Alsxilva/Azcatl/Documentación/Diagrama de clases/Diagrama de clases Azcatl.png

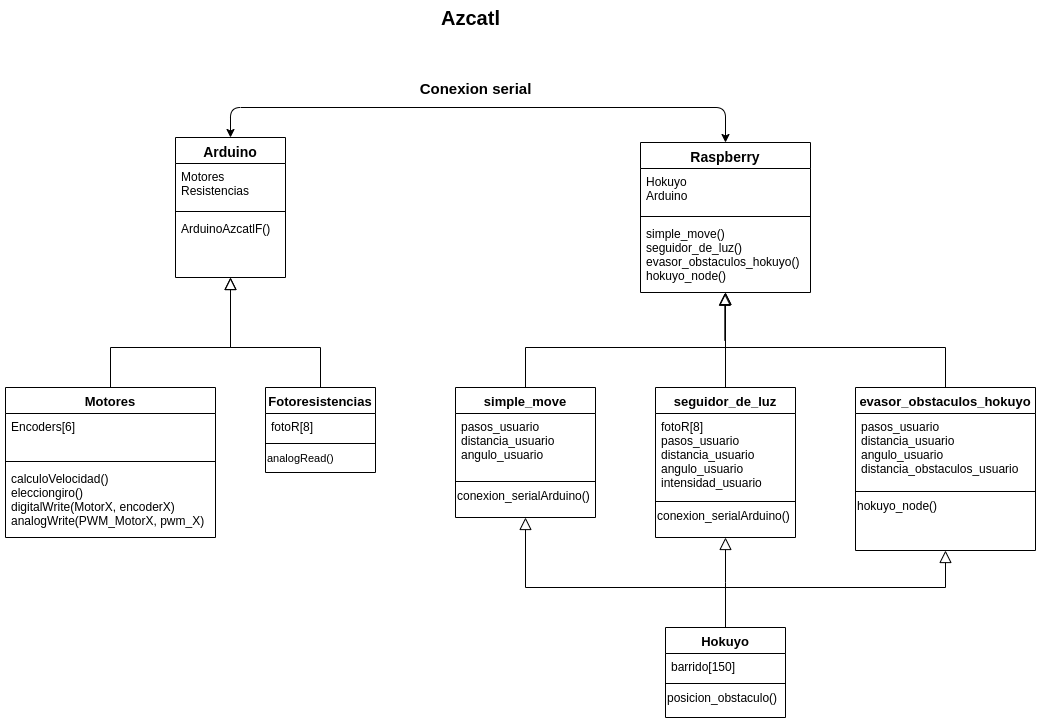
Documentación/Diagrama de clases/Diagrama de clases Azcatl.png
