Alsxilva/Azcatl/Documentación/Máquinas de estado/IMG_5838.JPG

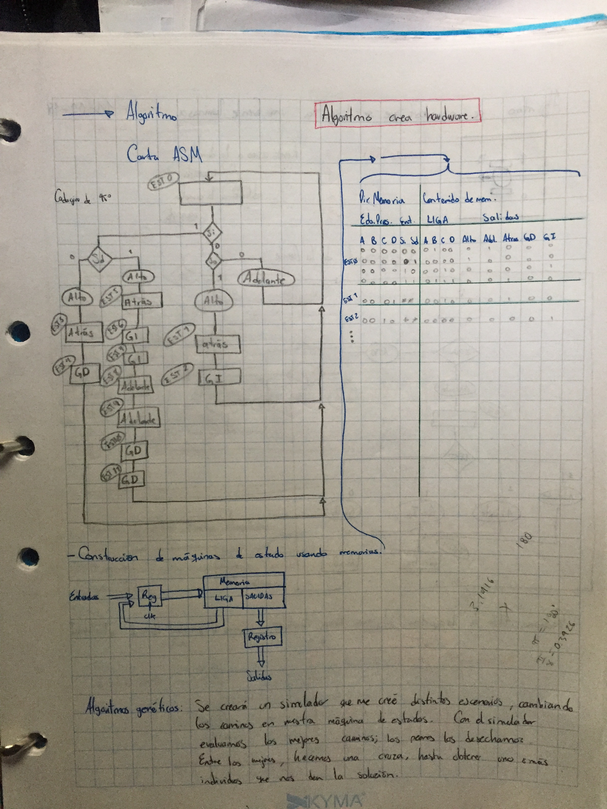
Documentación/Máquinas de estado/IMG_5838.JPG
