Alsxilva/Azcatl/Mis Nodos/evasor_obstaculos_hokuyo_FINAL.cpp

/*-------------------------------------------------------------
Silva Guzmán Alejandro
Dr. Savage Carmona
Agosto 2019

/*--------------------------------------------------------------*/

#include <time.h>
#include <math.h>
#include <stdlib.h>
#include <ros/ros.h>
#include <std_msgs/Int64.h>
#include <std_msgs/Float32.h>
#include <sensor_msgs/LaserScan.h>
#include <std_msgs/Float32MultiArray.h>
	
#define k 			0.1				//Constante de desfase 
#define vm			0.50			//Velocidad maxima [m/s]
#define bw  		0.235			//Ancho de la base del robøt  			[m]
#define ppr			1636.0			//Pulsos por revolucion (Encoder)
#define c_llant 	41.469 			//Circunferencia de cada llantas 		[cm]
#define d_llants	23.50000		//Distancia entre llantas contrarias 	[cm]
#define pi 			3.1415926		//Valor de pi

bool act = false;			 		//Bool para impedir que se avance mientras se gira y viceversa.
bool turnOn = false; 				//(Encender) Bool para evitar que en el primer case avance un paso sin revisar obstaculos-
volatile float enc[2]={0.0,0.0};

/*------------------------------------Encoders------------------------------------*/	

void callbackDer(const std_msgs::Int64::ConstPtr& msg){
	enc[1] = (float)(msg -> data)/ppr;							//Encoder 1 = Encoder derecho
	//printf("%li\n",msg -> data);								//Imprime el valor (float) del encoder
}

void callbackIzq(const std_msgs::Int64::ConstPtr& msg){
	enc[0] = (float)(msg -> data)/ppr;							//Encoder 0 = Encoder izquierdo
	//printf("%li\n",msg -> data);								//Imprime el valor (float) del encoder
	act = true;
}

/*------------------------------------Hokuyo------------------------------------*/	

/*--------------------------------Variables--------------------------------*/	

#define maxRange   80			//Rango de lecturas para el hokuyo
#define minRange  -80								
#define intervalRange  10 		//Grados para cada intervalo

int nuSamples;	 				//Numero de muestras que muestrearemos para detectar el obstaculo mas delgado
int truReadings = 0;				//Contador para obstaculos
int posicion_obstaculo;			//Indica la posicion del obstaculo
float umbral;					//Rango para determinar si se encuentra un obstaculo en determinada posicion
float umbral_usuario;		
float degrees_to_Sample;		//Grados a muestrear para el obstaculo mas delgado con base a la distancia a la que se encuentre y a su ancho
float obstacle_Width;			//Ancho del obstáculo más delgado a detectar	
float promLeft  =	 0;
float promRight =	 0;
float promFront =	 0;
float centralOut, derechaOut, izquierdaOut;
float values[2][(maxRange - minRange) / intervalRange];	//Dos arreglos de 16 valores cada uno

bool hokuyoFlag = false;
bool central_flag, centralDer_flag, centralIzq_flag, derecha_flag, izquierda_flag;		//Banderas para determinar zona de obstaculo

/*--------------------------------Funcion--------------------------------*/	

void callbackHokuyo(const sensor_msgs::LaserScan::ConstPtr &msg){

	int size = ceil((msg -> angle_max - msg -> angle_min) / msg -> angle_increment);	//Redondea al entero de arriba mas cercano. 
	//	size = ceil(593.8181818) = 594 lecturas											//En especifico, redondea a un numero entero el numero de lecturas 
																						//"disponibles" del hokuyoque se mandan desde el nodo "hokuyo_node.py"							
	float sumLeft  = 0;																	
	float sumFront = 0;	
	float sumRight = 0;	
	float values[size];
	
	for(int i = 0 ; i < size ; i++){			//Almacena los valores del hokuyo en un arreglo
		float val = msg -> ranges[i];
		values[i] = msg -> ranges[i];
		
		if(val <= 0.01 && i!=0)					//Evita que se se almacenen valores muy pequeños
			values[i] = 1.2 * values[i-1];
			//float angle = (msg->angle_min+(msg->angle_increment*i))*180.0/3.1415926;
	}

	/*-------------------------------Region central-------------------------------*/

	int centrali[2];
	centralOut = 0;
	float central[]  = {-15,15};		//Rangos para la region central -> Checar documento "Estructura del robot".
		
	centrali[0] = floor((((pi * central[0]) / 180.0) - msg->angle_min) / (msg->angle_increment));	//floor((((pi * -15) / 180) - 1.824262524000698) / 0.006144178739745) = floor(-339.5184288) = -339
	centrali[1] = floor((((pi * central[1]) / 180.0) - msg->angle_min) / (msg->angle_increment));	//floor((((pi *  15) / 180) - 1.824262524000698) / 0.006144178739745) = floor(-254.2997530) = -254
				//Funcion "floor" redondea al entero de abajo mas cercano
				//Esta fracción de codigo se encarga de transformar el ángulo de visión deseado por región a un número (en radianes) para que el hokuyo sea capaz de leerlo.
	
	for(int i = centrali[0]; i < centrali[1]; i++){
		if (values[i] <= umbral)
			truReadings ++;
		else 
			truReadings = 0;
		if (truReadings >= nuSamples){
			central_flag = true;
			truReadings = 0;
			break;
		}
		else
			central_flag = false;
	}

	/*---------------------------Region Izquierda---------------------------*/

	int izquierdai[2];
	izquierdaOut = 0;
	float izquierda[] ={45,75};		//Rangos para la region izquierda -> Checar documento "Estructura del robot".

	izquierdai[0] = floor((((pi * izquierda[0]) / 180.0)-msg->angle_min) / (msg->angle_increment));		//floor((((pi * 45) / 180) - 1.824262524000698) / 0.006144178739745) = floor(-169.0810773) = -169
	izquierdai[1] = floor((((pi * izquierda[1]) / 180.0)-msg->angle_min) / (msg->angle_increment));		//floor((((pi * 75) / 180) - 1.824262524000698) / 0.006144178739745) = floor(-83.86240161) = -83
	
	for(int i = izquierdai[0]; i < izquierdai[1] ; i++){
		if (values[i] <= umbral)
			truReadings ++;
		else 
			truReadings = 0;
		if (truReadings >= nuSamples){
			izquierda_flag = true;
			truReadings = 0;
			break;
		}
		else
			izquierda_flag = false;
	}

	/*---------------------------Region Derecha---------------------------*/

	int derechai[2];
	derechaOut = 0;
	float derecha[] ={-45,-75}; 	//Rangos para la region derecha -> Checar documento "Estructura del robot".
		
	derechai[0] = floor((((pi * derecha[0]) / 180.0)-msg->angle_min)/(msg->angle_increment));		//floor((((pi * -45) / 180) - 1.824262524000698) / 0.006144178739745) = floor(-424.7371045) = -424	
	derechai[1] = floor((((pi * derecha[1]) / 180.0)-msg->angle_min)/(msg->angle_increment));		//floor((((pi * -75) / 180) - 1.824262524000698) / 0.006144178739745) = floor(-509.9557802) = -509
	
	for(int i = derechai[1]; i < derechai[0] ; i++){
		if (values[i] <= umbral)
			truReadings ++;
		else 
			truReadings = 0;
		if (truReadings >= nuSamples){
			derecha_flag = true;
			truReadings = 0;
			break;
		}
		else
			derecha_flag = false;
	}

	/*---------------------------Posicion de obstaculo---------------------------*/	

																//estado de banderas
	if 		(!izquierda_flag & !derecha_flag & !central_flag)	//000
		posicion_obstaculo = 0;
	else if (!izquierda_flag & !derecha_flag & central_flag)	//001
		posicion_obstaculo = 1;
	else if (!izquierda_flag & derecha_flag & !central_flag)	//010
		posicion_obstaculo = 2;
	else if (!izquierda_flag & derecha_flag & central_flag)		//011
		posicion_obstaculo = 3;
	else if (izquierda_flag & !derecha_flag & !central_flag)	//100
		posicion_obstaculo = 4;
	else if (izquierda_flag & !derecha_flag & central_flag)		//101
		posicion_obstaculo = 5;
	else if (izquierda_flag & derecha_flag & !central_flag)		//110
		posicion_obstaculo = 6;
	else if (izquierda_flag & derecha_flag & central_flag)		//111
		posicion_obstaculo = 7;
	else 														//???
		posicion_obstaculo = 8;
	

	/*---------------------------EndRangos---------------------------*/	
	//printf("\n\nLecturas (size) = %d",size);
	hokuyoFlag = true;
}

void data_hokuyo(){
	/*---------------------------Datos obtenidos---------------------------*/
	//Imprime datos obtenidos dentro de los rangos definidos. 
	//Imprimira "False" si dentro de esa region NO hay obstaculoTrue
	//Imprimira "True " si dentro de esa region SI hay obstaculo
	printf("\n\nUmbral:\t\t%.4f\t\t[m]\tObstacle?",umbral);
	printf("\nIzquierda:\t%.4f\t\t[m]\t",	izquierdaOut); 	printf(izquierda_flag 	? "True" : "False");
	printf("\nCentral:\t%.4f\t\t[m]\t",		centralOut);	printf(central_flag 	? "True" : "False");
	printf("\nDerecha:\t%.4f\t\t[m]\t",		derechaOut);	printf(derecha_flag 	? "True" : "False");
	printf("\n");
	//printf("\nCentral Izq:\t%.4f\t",	centralIzqOut); printf(centralIzq_flag 	? "False" : "True");
	//printf("\nCentral Der:\t%.4f\t",	centralDerOut);	printf(centralDer_flag	? "False" : "True");
}

/*------------------------------------Inicio del Main------------------------------------*/	

int main(int argc, char ** argv){
	ros::init(argc, argv, "evasor_obstaculos_hokuyo");	//Inicio de ROS. Necesarios Argc y Argv. Tercer argumento: nombre del nodo.
	ros::NodeHandle nh;						//Manipulador de nodos: nodo publico 
	ros::Rate rate(20);						//Tasa/cantidad de frecuencia 
	
	/*------------------------------------Se instancian subscriptores y publicadores------------------------------------*/	

	ros::Subscriber subHokuyo   	= nh.subscribe("/scan",1,callbackHokuyo);						//Regresa ROS subscriber y avisa a ROS la 'lectura'
	ros::Subscriber encoizq 		= nh.subscribe("/encoIzq",1,callbackIzq);						//de mensajes y como maximo 1 mensaje en el buffer. 
	ros::Subscriber encoder 		= nh.subscribe("/encoDer",1,callbackDer);			
																									
	ros::Publisher pubVelMotor 	= nh.advertise<std_msgs::Float32MultiArray>("/motor_speeds",1);		//Regresa ROS publisher y avisa a ROS la 'publicacion'  				
																									//de mensajes y como maximo 1 mensaje en el buffer.
	int disOffset	;
	float dist, angle;
	float distancia_usuario, angulo_usuario;
	std_msgs::Float32MultiArray msg;		//Variable que almacena mensaje que vamos a enviar 
	msg.data.resize(2);						//Tamaño de la variable msg

	while(ros::ok()){						//Ejecuta ROS mientras no exista alguna interrupción.
		
/*------------------------------------Maquina de estados para evadir obstaculos------------------------------------*/	

		srand(time(NULL));			//Funcion para generar numeros aleatorios
		int pot;					//Variable que almacena numero aleatorio
		int num = -1;				//Numero que se elevará a la potencia -pot- y determinara el sentido del giro
		
		int total_steps, step=0;
		printf( "\033[2J\033[1;1H" );		
		printf("\n------------------------ Evasor de Obstaculos -------------------------");	
		printf("\n-------------------------------- START --------------------------------",step+1,total_steps);
		printf("\n\nIntroduzca:\n\nEl numero de pasos deseado [entero]: ");
		scanf("%d",&total_steps);
		printf("Angulo a girar por paso [°]: ");
		scanf("%f",&angulo_usuario);
		printf("Distancia a recorrer por paso [cm]: ");
		scanf("%f",&distancia_usuario);
		printf("Distancia a detectar los obstaculos [cm]: ");
		scanf("%f",&umbral_usuario);
		printf("Ancho del obstaculo mas delgado a detectar [cm]: ");
		scanf("%f",&obstacle_Width);
		
		degrees_to_Sample = (obstacle_Width * 360) / (2 * pi * umbral_usuario);
		nuSamples = floor(degrees_to_Sample / 0.352);

		umbral = umbral_usuario/100;
		step = 0;
		int next_state = 0;				//Inicia maquina de estados

		while (step < total_steps ){

			hokuyoFlag = false;						//Bandera para detectar la conexion con el hokuyo
			printf("\n\n--->Esperando a Hokuyo.");
			
			while(!hokuyoFlag && ros::ok()){
				printf("..");					//Imprimira ".." mientras espera respuesta de Hokuyo
				ros::spinOnce();
				rate.sleep();
			} 
			printf( "\033[2J\033[1;1H" );
			printf("\n------------------------------Step: %d de: %d------------------------------",step+1,total_steps);

			switch(next_state){
				case 0:
					if (posicion_obstaculo == 0){			// Sin obstaculo enfrente, avanza
						angle = 0;
						dist = distancia_usuario;
                        printf("\n\n----->Sin obstaculo");
                        data_hokuyo();
						step++;
                        next_state = 0;
                        turnOn = true;
                        break;
	                }
	                else{
	                	turnOn = false;
                        if		(posicion_obstaculo == 1){		
                            printf("\n\n----->Obstaculo al frente");
                            data_hokuyo();
                            next_state = 5;
                            break;
                        }
                        else if (posicion_obstaculo == 2){		
                            printf("\n\n----->Obstaculo a la derecha");
                            data_hokuyo();
                            next_state = 1;
                            break;
                        }
                        else if (posicion_obstaculo == 3){		
                            printf("\n\n----->Obstaculo enfrente y a la derecha");                          
                  		    data_hokuyo();
                            next_state = 1;
                            break;
                        }
                        else if (posicion_obstaculo == 4){		
                            printf("\n\n----->Obstaculo a la izquierda");
                            data_hokuyo();
                            next_state = 3;
                            break;
                        }
                        else if (posicion_obstaculo == 5){		
                            printf("\n\n----->Obstaculo enfrente y a la izquierda");
                            data_hokuyo();
                            next_state = 3;
                            break;
                        }
                        else if (posicion_obstaculo == 6){		
                            printf("\n\n----->Obstaculo a la derecha e izquierda");
                            data_hokuyo();
                            next_state = 5;
                            break;
                        }
                        else if (posicion_obstaculo == 7){		
                            printf("\n\n----->Obstaculo enfrente, derecha e izquierda");
                            data_hokuyo();
                            next_state = 5;
                            break;
                        }
                        else if (posicion_obstaculo == 8){		
                            printf("\n\n-----> Otro caso 1:\t%c", posicion_obstaculo);
                            data_hokuyo();
                            step = total_steps;		//Termina ejecucion del algoritmo en caso de error
                            printf("\n\n-----> ERROR");
                            break;
                        }
                        else {
                        	printf("\n\n-----> Otro caso 2:\t%c", posicion_obstaculo);
                        	data_hokuyo();
                        	step = total_steps;		//Termina ejecucion del algoritmo en caso de error
                        	printf("\n\n-----> ERROR");
                        	break;
                        }
	                }
					break;

				/*---------------------------Obstaculo en la derecha---------------------------*/
					
				case 1: 			// Reversa
					printf("\n\n----->Obstaculo a la derecha");
                    data_hokuyo();
	                printf("\n\n--->Case 1: Reversa\n");
	                angle = 0;
					dist = -distancia_usuario;
	                next_state = 2;
	                turnOn = true;
               		break;

		        case 2: 			// Giro izquierdo
		        	printf("\n\n----->Obstaculo a la derecha");
                    data_hokuyo();
	                printf("\n\n--->Case 2: Giro izquierdo\n");
	                angle = angulo_usuario;
					dist = 0;
	                next_state = 0;
	                step++;
	                break;

	            /*---------------------------Obstaculo en la izquierda---------------------------*/

		        case 3: 			// Reversa
		        	printf("\n\n----->Obstaculo a la izquierda");
                    data_hokuyo();
	                printf("\n\n--->Case 3: Reversa\n");
	                angle = 0;
					dist = -distancia_usuario;
	                next_state = 4;
	                turnOn = true;
	                break;

		        case 4: 			// Giro derecho
		        	printf("\n\n----->Obstaculo a la izquierda");
                    data_hokuyo();
	                printf("\n\n--->Case 4: Giro derecho\n");
	                angle = -angulo_usuario;
					dist = 0;
	                next_state = 0;
	                step++;
	                break;

	            /*---------------------------Obstaculo al frente---------------------------*/

		        case 5: 			// Reversa
		        	printf("\n\n----->Obstaculo al frente");
                    data_hokuyo();
	                printf("\n\n--->Case 5: Reversa\n");
	                angle = 0;
					dist = -distancia_usuario;
	                next_state = 6;
	                turnOn = true;
	                pot = rand()%11;
	                num = pow (num, pot);
	                break;

		        case 6: 			// Giro aleatorio
		        	printf("\n\n----->Obstaculo al frente");
                    data_hokuyo();
	                printf("\n\n--->Case 6: Giro");
	                angle = angulo_usuario * num;
	                if (angle < 0)
	                    printf(" a la derecha\n");
	                else 
	                	printf(" a la izquierda\n");
					dist = 0;
	                next_state = 7;
	                break;

		        case 7:				// Giro aleatorio
		        	printf("\n\n----->Obstaculo al frente");
                    data_hokuyo();
                    printf("\n\n--->Case 7: Giro");
	                angle = angulo_usuario * num;
	                if (angle < 0)
	                    printf(" a la derecha\n");
	                else
	                	printf(" a la izquierda\n");
	                angle = angulo_usuario * num;
					dist = 0;
	                next_state = 8;
	                break;

		        case 8: 			// Avanza
		        	printf("\n\n----->Obstaculo al frente");
                    data_hokuyo();
	                printf("\n\n--->Case 8: Avanza\n");
	                angle = 0;
					dist = distancia_usuario;
	                next_state = 9;
	                break;

		        case 9: 			// Giro contrario al aleatorio
		        	printf("\n\n----->Obstaculo al frente");
                    data_hokuyo();
	                angle = angulo_usuario * -num;
	                printf("\n\n--->Case 9: Giro");
	                if (angle < 0)
	                    printf(" a la derecha\n");
	                else
	                	printf(" a la izquierda\n");
					dist = 0;
	                next_state = 10;
	                break;

		        case 10: 			// Giro contrario al aleatorio
		        	printf("\n\n----->Obstaculo al frente");
	                data_hokuyo();
	                angle = angulo_usuario * -num;
	                printf("\n\n--->Case 10: Giro");
	                if (angle < 0)
	                    printf(" a la derecha\n");
	                else
	                	printf(" a la izquierda\n");
					dist = 0;
	                next_state = 0;
	                step++;
	                break;
 			}

 			if (turnOn){		//Indica al robot, ahora sí, comenzar movimiento

	 			/*-----------------Inserción de valores: angulo de giro y distancia-----------------*/

				angle *= -1.9;						//Factor de corrección.
				dist  *=  0.9;						//Factor de corrección.

				/*--------------------------Giro--------------------------*/	

				float angulo = angle;
				int anterior = enc[0];				//Variable para determinar si cambio orientacion de la llanta
				int actual   = enc[0] + 100;		//Variable para determinar si cambio orientacion de la llanta


				//-------------------Parámetros usados en el perfil trapezoidal de giro-----------------------*/	

				float inicio  = enc[0];														//Posicion inicial del encoder derecho
				float posIzq0 = enc[0];														//Posición actual del encoder 0: izquierdo
				float posDer0 = enc[1];														//Posición actual del encoder 1: derecho
				float posIzqFin = posIzq0 + ((d_llants * pi * angulo) / (c_llant * 360.0));	//Posiciones finales de los encoders
				float posDerFin = posDer0 + ((d_llants * pi * angulo) / (c_llant * 360.0));	//a las que se quiere llegar.
				float delta   = posIzqFin - posIzq0;										//Distancia a avanzar = distancia sobre circunferencia de llantas: número de vueltas por llanta para alcanzar la distancia 
				float limite1 = (delta / 3.0) + posIzq0;									//Primer segmento que recorre el robot: un tercio de la diferencia de pi y pf mas la posición inicial 
				float limite2 = (delta * (2.0 / 3.0)) + posIzq0;							//Segundo segmento que recorre el robot: dos tercios de la diferencia de pi y pf mas la posicion inicial

				//printf("%f %f \n",enc[0],limite1);

				if(angulo > 0.001){		//Para angulo mayor a cero (rotación a la derecha)
					
					//-------------------Loop para seguir recibiendo datos-----------------------/	

					while(anterior != actual){
						act = false;
						printf("\n--->Esperando motores 1.");
						while(!act && ros::ok()){				
							printf("..");
							//printf("\nEncoder derecho  : %.4f", enc[1]);
							//printf("\nEncoder izquierdo: %.4f", enc[0]);
							ros::spinOnce();								//Recibe llamadas de vuelta al subscriber
							rate.sleep();									//Espera mientras el mensaje es emitido
						}
						anterior = actual;			//Actualiza valores de los encoders
						actual = enc[0];			//para la siguiente comprobacion
					}
				//-----------------------------Perfil trapezoidal-----------------------------------*/	

					//-----------------Primera parte del perfil trapezoidal-----------------------*/	

					printf("\n\n--->Dare giro a la derecha");
					printf("\n------->Grados = %.3f [°]",angulo_usuario);

					while(enc[0] < limite1 && ros::ok()){
						//printf("%f %f \n",enc[0],limite1);
						//printf("\n\n--->Giro Derecha 1");
						msg.data[0] = k + (3.0 * (vm - k) * (fabs(enc[0] - posIzq0)/(delta)));		//Las llantas del lado izquierdo giran hacia adelante
					    msg.data[1] = -msg.data[0];													//mientras que las del lado derecho hacia atras.
			       		pubVelMotor.publish(msg);		//Emite mensaje con la velocidad de los motores
						ros::spinOnce();
						rate.sleep();		
					}

					//-----------------Segunda parte del perfil trapezoidal-----------------*/	

					while(enc[0] < limite2 && ros::ok()){
						//printf("\n--->Giro Derecha 2");
						msg.data[0] = vm;				//Alcanza velocidad máxima
						msg.data[1] = -vm;	
			       		pubVelMotor.publish(msg);
						ros::spinOnce();
						rate.sleep();		
					}

					//-----------------Tercera parte del perfil trapezoidal-----------------*/	

					while(enc[0] < posIzqFin && ros::ok()){
						//printf("\n--->Giro Derecha 3");
						//printf("%f %f \n",enc[0],posIzqFin);
						msg.data[0] = vm - (3.0 * (vm - k) * ((fabs(enc[0] - posIzq0) / (delta)) - (2.0 / 3.0)));
						msg.data[1] = -msg.data[0];
			       		pubVelMotor.publish(msg);
						ros::spinOnce();
						rate.sleep();		
					}

					printf("\n\n---Termine de girar a la derecha---");

				}else if (angulo < -0.001){				//Para angulo menor a cero (rotacion a la izquierda)
					
					//-------------------Loop para seguir recibiendo datos-----------------------/
					while(anterior != actual){
						act = false;
						printf("\n--->Esperando motores 1.");
						while(!act && ros::ok()){				
							printf("..");
							//printf("\nEncoder derecho  : %.4f", enc[1]);
							//printf("\nEncoder izquierdo: %.4f", enc[0]);
							ros::spinOnce();								//Recibe llamadas de vuelta al subscriber
							rate.sleep();									//Espera mientras el mensaje es emitido
						}
						anterior = actual;			//Actualiza valores de los encoders
						actual = enc[0];			//para la siguiente comprobacion
					}

					//---------------------------Perfil trapezoidal---------------------------*/	

					//-----------------Primera parte del perfil trapezoidal-----------------*/	

					printf("\n\n--->Dare giro a la izquierda");
					printf("\n------->Grados = %.3f [°]",angulo_usuario);
					
					while(enc[0] > limite1 && ros::ok()){
						//printf("\n\n--->Giro Izquierda 1");
						msg.data[0] = (-k - (3.0 * (vm - k) * (-fabs(enc[0] - posIzq0)/(delta))));		//Las llantas del lado derecho giran hacia adelante
						msg.data[1] = - msg.data[0];													//mientras que las del lado izquierdo hacia atras.
						pubVelMotor.publish(msg);
						ros::spinOnce();
						rate.sleep();
					}

					//-----------------Segunda parte del perfil trapezoidal-----------------*/	

					while(enc[0] > limite2 && ros::ok()){
						//printf("\n--->Giro Izquierda 2");
						msg.data[0] = -vm;
						msg.data[1] = vm;						//Alcanza velocidad máxima
						pubVelMotor.publish(msg);
						ros::spinOnce();
						rate.sleep();
					}

					//-----------------Tercera parte del perfil trapezoidal-----------------*/	

					while(enc[0] > posIzqFin && ros::ok()){
						//printf("\n--->Giro Izquierda 3");
						msg.data[0] = -(((vm - k) / (delta * 0.33333 *-1)) * (enc[0] - posIzqFin)) - k;
						msg.data[1] = -msg.data[0];
						pubVelMotor.publish(msg);
						ros::spinOnce();
						rate.sleep();
					}
					printf("\n\n---Termine de girar a la izquierda---");
				}

				
				/*----------------------------Reset de encoders----------------------------*/	
				for(int i = 0; i<10 ; i++){
					msg.data[0] = 0.0;
					msg.data[1] = 0.0;
					pubVelMotor.publish(msg);
					ros::spinOnce();
					rate.sleep();
				}	
				//rate.sleep();							//Duerme al robot, determinado por la frecuencia indicada (20 Hz)
				//ros::Duration(1.0).sleep();				//Duerme al robot por un segundo
				
				/*--------------------------------------Avance--------------------------------------*/
					
				//printf("Comenzando el avance...");
				float av = 10;
				av 	= dist;
				act = false;
				actual = enc[0] + 100;


				//-------------------Parámetros usados en el perfil trapezoidal de avance positivo-------------------*/	
				
				posIzq0 = enc[0];								//Posición actual del encoder 0: izquierdo
				posDer0 = enc[1];								//Posición actual del encoder 1: derecho
				delta   = av / c_llant;							//Distancia a avanzar = distancia sobre circunferencia de llantas: numero de vueltas por llanta para alcanzar la distancia deseada.
				posIzqFin = posIzq0 + (av / c_llant);			//Posiciones finales de los encoders
				posDerFin = posDer0 + (av / c_llant);			//a las que se quiere llegar.
				limite1 = (delta / 3.0) + posIzq0;				//Primer segmento que recorre el robot: un tercio de la diferencia de pi y pf mas la posicion inicial 
				limite2 = (delta * (2.0 / 3.0)) + posIzq0;		//Segundo segmento que recorre el robot: dos tercios de la diferencia de pi y pf mas la posicion inicial
				//printf("%f %f \n",enc[0],limite1);

				//---------------------------------------------Avance---------------------------------------------*/	

				if(av > 0.001){			//Si la distancia a moverse es positiva (hacia adelante)

					//-------------------Loop para seguir recibiendo datos-------------------//
					while(anterior != actual){
						act = false;
						printf("\n--->Esperando motores 2.");
						while(!act && ros::ok()){
							printf("..");
							//printf("\nEncoder derecho  : %.4f", enc[1]);
							//printf("\nEncoder izquierdo: %.4f", enc[0]);
							ros::spinOnce();
							rate.sleep();
						}
						anterior = actual;
						actual = enc[0];
					}

					printf("\n\n--->Avanzare:");
					printf("\n------->Distancia = %.3f [cm]",distancia_usuario);
					//printf("\n\tDistancia = %.3f [cm] %f",distancia_usuario, av);

					//printf("Comenzando movimiento hacia adelante...");
					//printf("Delta: %.4f \n",delta);
					//msg.data[0] = k;					//Desfase de inicio del perfil trapezoidal
					//msg.data[1] = k;
					//pubVelMotor.publish(msg);
					//ros::spinOnce();
					//rate.sleep();

					//---------------------------Perfil trapezoidal---------------------------*/	

					//-----------------Primera parte del perfil trapezoidal-----------------*/	


					while(enc[0] < limite1  && ros::ok()){
						//printf("%f %f %f \n",enc[0],limite1,msg.data[1]);
						//printf("\n\n--->Avance 1");
						float error = fabs(enc[0]- posIzq0); 
						//printf("\n**********%f-------------\n",error);
						msg.data[0] = k + (3.0 * (vm - k) * (fabs(enc[0] - posIzq0) / (delta)));		//Ambos secciones de llantas, izquierda
						msg.data[1] = msg.data[0];														//y derecha, giraran hacia adelante
						pubVelMotor.publish(msg);
						ros::spinOnce();
						rate.sleep();
					}

					//-----------------Segunda parte del perfil trapezoidal-----------------*/	

					while(enc[0] < limite2 && ros::ok()){
						//printf("%f %f %f\n",enc[0],limite2,vm);
						//printf("\n--->Avance 2");
						msg.data[0] = vm;
						msg.data[1] = msg.data[0];
						pubVelMotor.publish(msg);
						ros::spinOnce();
						rate.sleep();
					}

					//-----------------Tercera parte del perfil trapezoidal-----------------*/	

					while(enc[0] < posIzqFin && ros::ok()){
						//printf("%f %f %f\n",enc[0],posIzqFin,msg.data[1]);
						//printf("\n--->Avance 3");
						msg.data[0] = vm - (3.0 * (vm - k) * ((fabs(enc[0] - posIzq0) / (delta)) - (2.0 / 3.0)));
						msg.data[1] = msg.data[0];
						pubVelMotor.publish(msg);
						ros::spinOnce();
						rate.sleep();
					}

					printf("\n----Termine de avanzar----");

				//-----------------------------------------------Retroceso-----------------------------------------------*/	

				}else if(av < -0.001){		//Si la distancia a moverse es negativa (reversa)

					//-------------------Loop para seguir recibiendo datos-------------------//
					while(anterior != actual){
						act = false;
						printf("\n--->Esperando motores 2.");
						while(!act && ros::ok()){
							printf("..");
							//printf("\nEncoder derecho  : %.4f", enc[1]);
							//printf("\nEncoder izquierdo: %.4f", enc[0]);
							ros::spinOnce();
							rate.sleep();
						}
						anterior = actual;
						actual = enc[0];
					}

					//---------------------------Perfil trapezoidal---------------------------*/

					//-----------------Primera parte del perfil trapezoidal-----------------*/	

					printf("\n\n--->Retrocedere:");
					printf("\n------->Distancia = %.3f [cm]",distancia_usuario);

					while(enc[0]>limite1 && ros::ok()){
						//printf("%f %f %f\n",enc[0],limite1,msg.data[0]);
						//printf("\n ********%f*****+ \n",(enc[0]-posIzq0));
						//printf("\n\n--->Reversa 1");
						msg.data[0] =(-k - (3.0 * (vm - k) * (-fabs(enc[0] - posIzq0) / (delta))));		//Ambas secciones de llantas, izquierda
						msg.data[1] = msg.data[0];														//y derecha, giran hacia atras
						pubVelMotor.publish(msg);
						ros::spinOnce();
						rate.sleep();
					}

					//-----------------Segunda parte del perfil trapezoidal-----------------*/	

					while(enc[0] > limite2 && ros::ok()){
						//printf("%f %f %f\n",enc[0],limite2,-vm);
						//printf("\n--->Reversa 2");
						msg.data[0] = -vm;
						msg.data[1] = msg.data[0];
						pubVelMotor.publish(msg);
						ros::spinOnce();
						rate.sleep();
					}

					//-----------------Tercera parte del perfil trapezoidal-----------------*/	

					while(enc[0] > posIzqFin && ros::ok()){
						//printf("%f %f %f\n",enc[0],posIzqFin,msg.data[1]);
						//printf("\n--->Reversa 3");
						msg.data[0] = -(((vm - k) / (delta * 0.33333 * -1)) * (enc[0] - posIzqFin)) - k;
						msg.data[1] = msg.data[0];
						pubVelMotor.publish(msg);
						ros::spinOnce();
						rate.sleep();
					}

					printf("\n\n----Termine de retroceder----");
				}

				/*----------------------------Reset de encoders----------------------------*/	
				for(int i = 0; i<10 ; i++){
					msg.data[0] = 0.0;
					msg.data[1] = 0.0;
					pubVelMotor.publish(msg);
					ros::spinOnce();
					rate.sleep();
				}
				rate.sleep();							//Duerme al robot, determinado por la frecuencia indicada (20 Hz)
				//ros::Duration(1.0).sleep();				//Duerme al robot por un segundo
 			}	
		}
		printf("\n\n\n--------------------------- TERMINE PASOS ----------------------------");
		ros::Duration(2.0).sleep();
	}
	return 0;
}
